tallnhairydave/LaundryBot/STL files/letter_l.stl

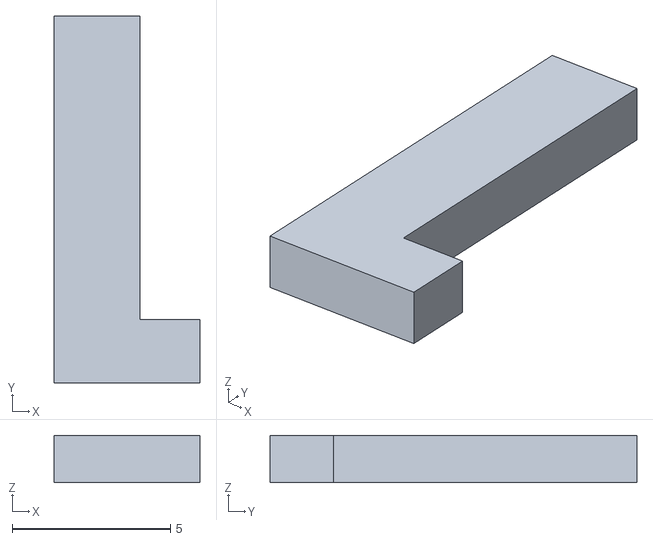
[picture p21: CAD file, 2021-01-31]
STL files/letter_l.stl
4.62 x 11.6 x 1.50
