tallnhairydave/LaundryBot/STL files/letter_o.stl

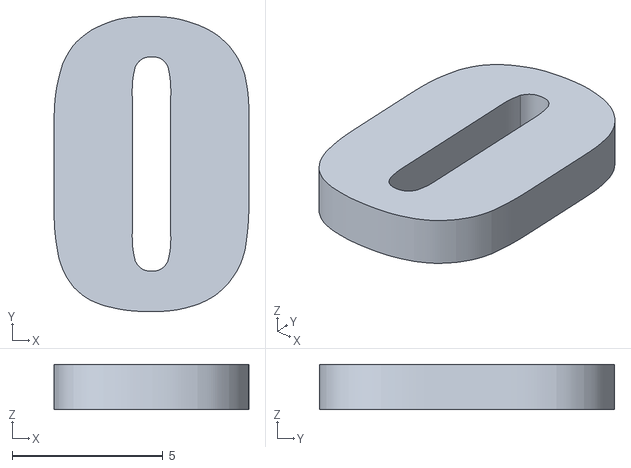
[picture p22: CAD file, 2021-01-31]
STL files/letter_o.stl
6.46 x 9.79 x 1.50
